jerryok826/Instrumentation-Audio-PWR-AMP/Pictures/IMG_7556.jpeg

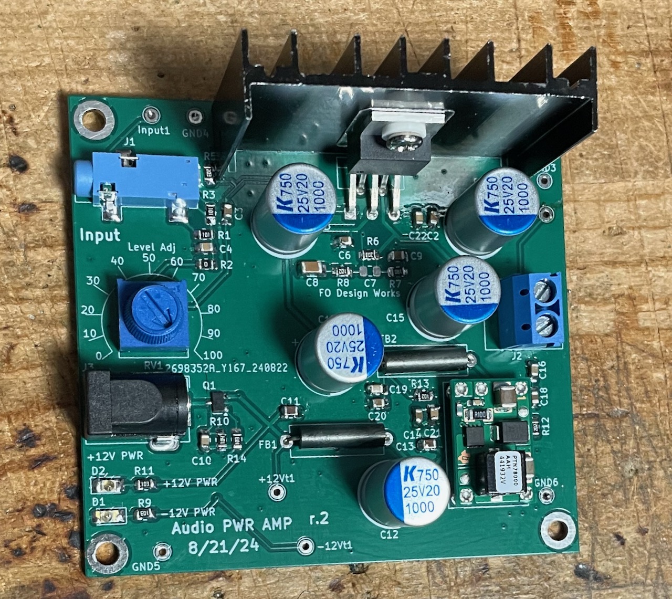
Pictures/IMG_7556.jpeg
